bigjosh/ThePresentMovement/waveforms/New movement power draw across 1 bat at 1 tick per sec.png

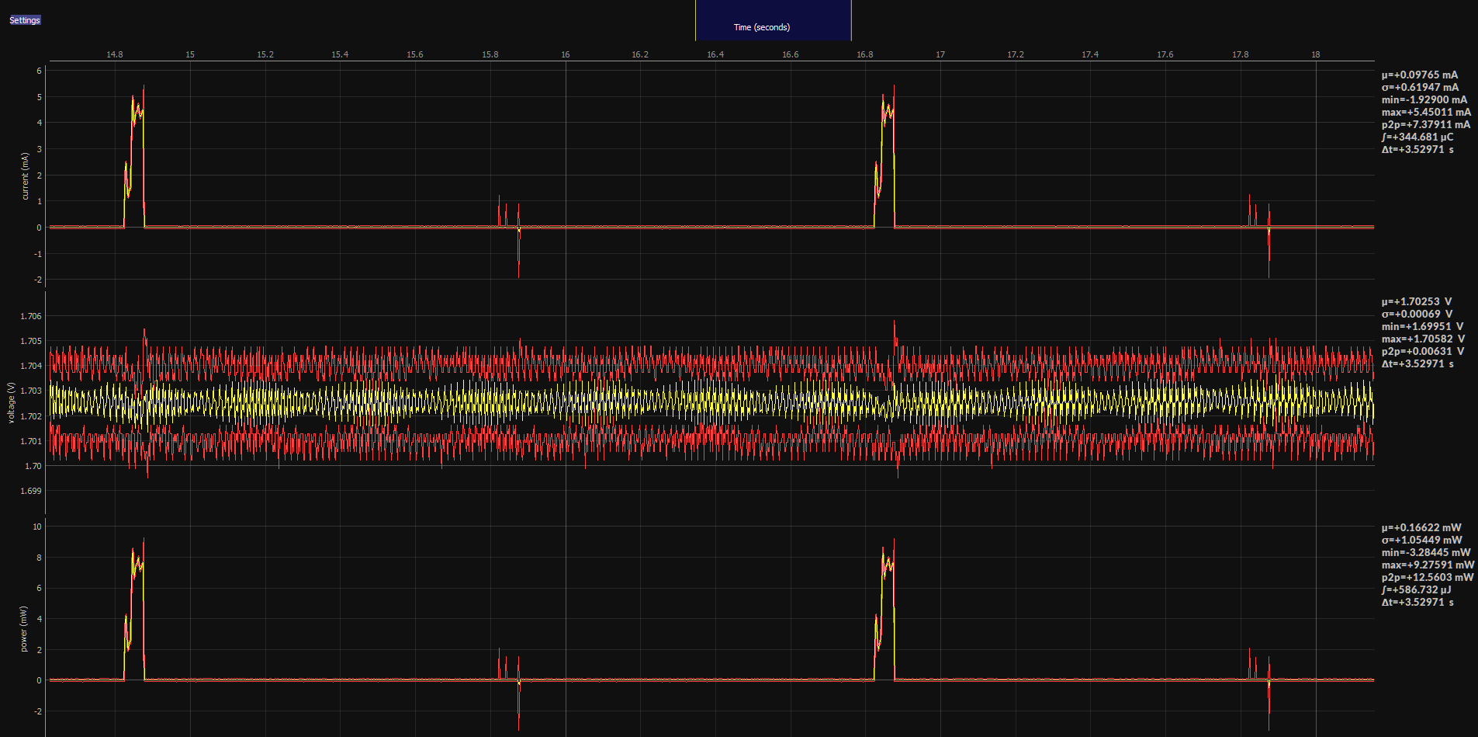
waveforms/New movement power draw across 1 bat at 1 tick per sec.png
