bigjosh/ThePresentMovement/waveforms/New movement power draw across 1 bat positive tick.png

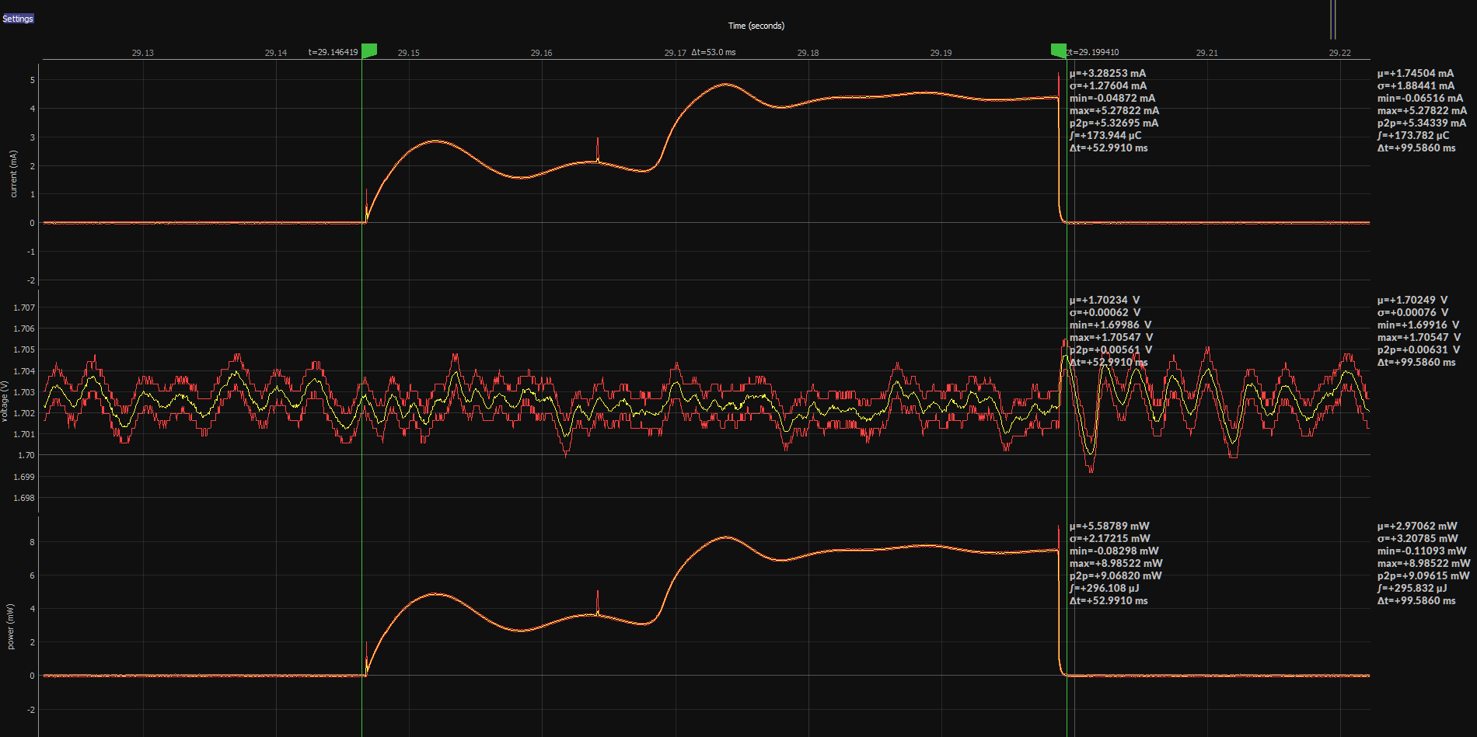
waveforms/New movement power draw across 1 bat positive tick.png
