bigjosh/ThePresentMovement/waveforms/New movement power draw between ticks.png

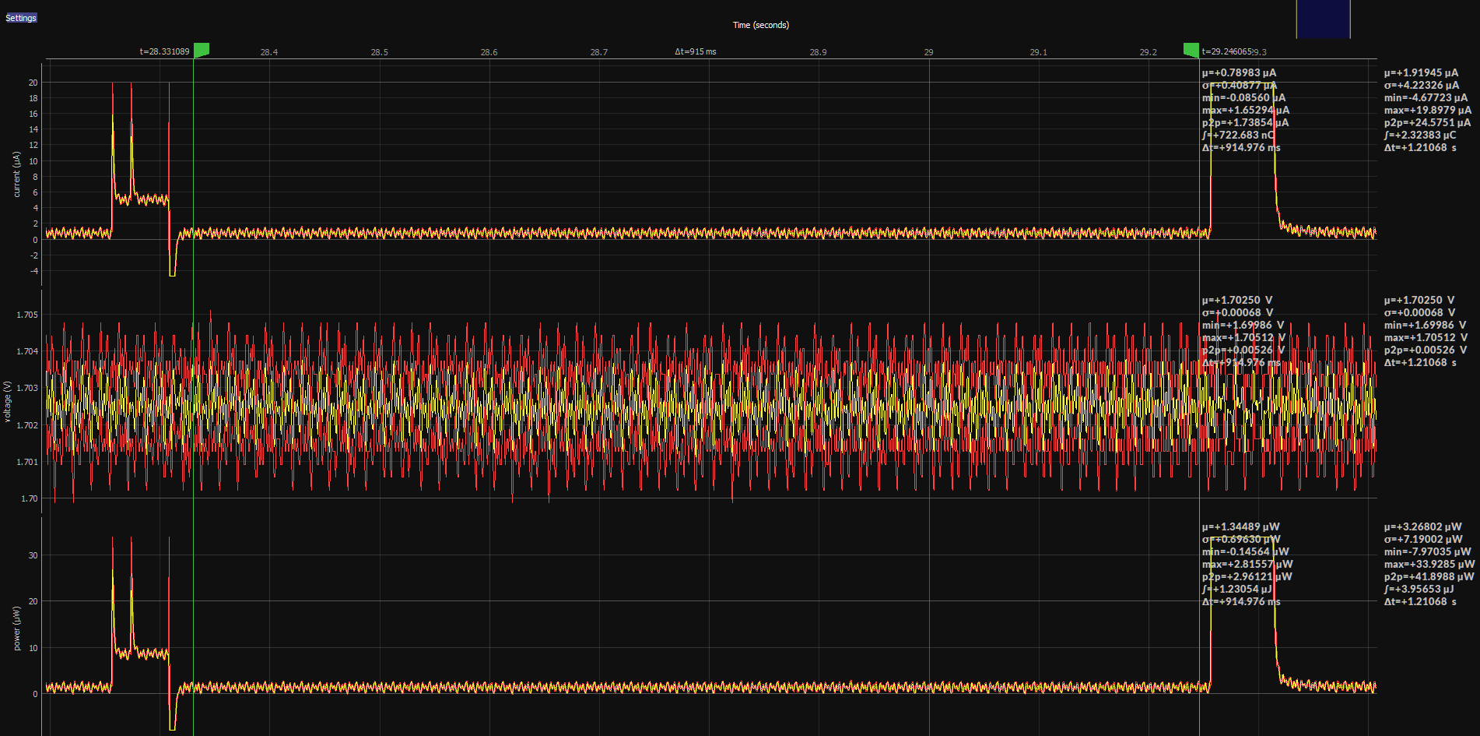
waveforms/New movement power draw between ticks.png
