bigjosh/ThePresentMovement/waveforms/new-v-no-coil.png

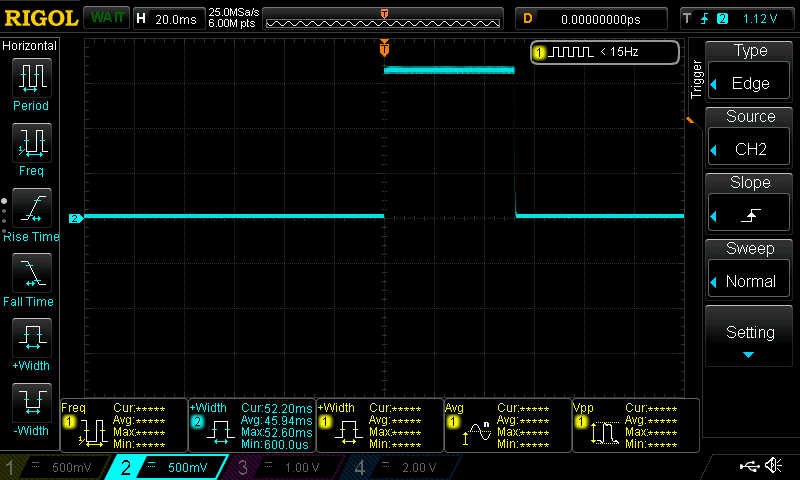
waveforms/new-v-no-coil.png
