bigjosh/ThePresentMovement/waveforms/Original Movement across motor negative.png

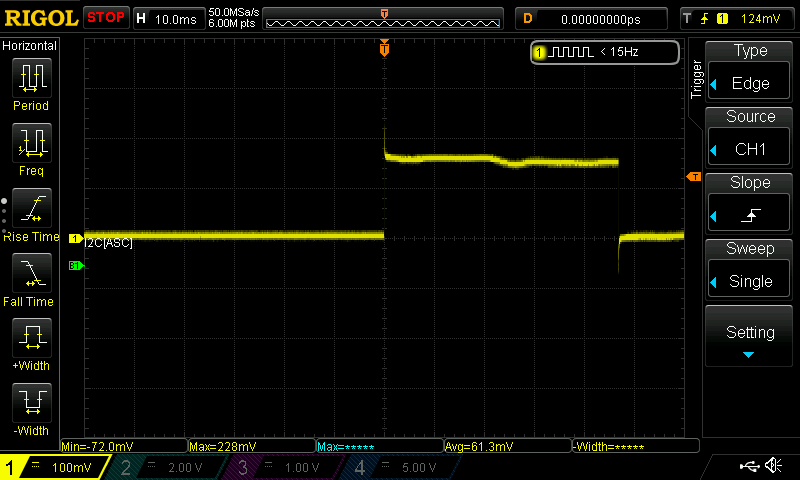
waveforms/Original Movement across motor negative.png
